alfanata/tictactoe-fpga/vhdl/tictactoe_ram.vhd

-- MIT License
-- 
-- Copyright (c) 2019 J. Tetteroo
-- 
-- Permission is hereby granted, free of charge, to any person obtaining a copy
-- of this software and associated documentation files (the "Software"), to deal
-- in the Software without restriction, including without limitation the rights
-- to use, copy, modify, merge, publish, distribute, sublicense, and/or sell
-- copies of the Software, and to permit persons to whom the Software is
-- furnished to do so, subject to the following conditions:
-- 
-- The above copyright notice and this permission notice shall be included in all
-- copies or substantial portions of the Software.
-- 
-- THE SOFTWARE IS PROVIDED "AS IS", WITHOUT WARRANTY OF ANY KIND, EXPRESS OR
-- IMPLIED, INCLUDING BUT NOT LIMITED TO THE WARRANTIES OF MERCHANTABILITY,
-- FITNESS FOR A PARTICULAR PURPOSE AND NONINFRINGEMENT. IN NO EVENT SHALL THE
-- AUTHORS OR COPYRIGHT HOLDERS BE LIABLE FOR ANY CLAIM, DAMAGES OR OTHER
-- LIABILITY, WHETHER IN AN ACTION OF CONTRACT, TORT OR OTHERWISE, ARISING FROM,
-- OUT OF OR IN CONNECTION WITH THE SOFTWARE OR THE USE OR OTHER DEALINGS IN THE
-- SOFTWARE.

-------------------------------------------------------------------------------
--
-- Title       : tictactoe_ram
-- Design      : tictactoe
-- Author      : J. Tetteroo
-- Year		   : 2019
--
-------------------------------------------------------------------------------

-------------------------------------------------------------------------------
--
-- Description : Memory unit that stores all possible game moves in native BRAM blocks (ice40 512x8) in 3 byte records.
--
-------------------------------------------------------------------------------

library ieee;
library work;
--library ice;	-- uncomment for simulation, comment for synthesis
use ieee.std_logic_1164.all;
--use ice.vcomponent_vital.all; -- uncomment for simulation, comment for synthesis



use work.components.all; 	-- comment for simulation, uncomment for synthesis
use work.tictactoe_global.all;
use ieee.numeric_std.all;

entity tictactoe_ram is
port (
    input : in tictactoe_ram_input_type;
    output : out tictactoe_ram_output_type;
    
    clk : in std_logic;
    reset : in std_logic
    );
end tictactoe_ram;




architecture rtl of tictactoe_ram is 

	-- ### START COMMENT BLOCK FOR SYNTHESIS (comment this block when synthesizing)
	-- Component declaration of the "sb_ram512x8(sb_ram512x8_arch)" unit defined in
	-- file: "./src/sb_ice_syn_vital.vhd"
--	component sb_ram512x8
--	generic(
--		INIT_0 : BIT_VECTOR := X"0000000000000000000000000000000000000000000000000000000000000000";
--		INIT_1 : BIT_VECTOR := X"0000000000000000000000000000000000000000000000000000000000000000";
--		INIT_2 : BIT_VECTOR := X"0000000000000000000000000000000000000000000000000000000000000000";
--		INIT_3 : BIT_VECTOR := X"0000000000000000000000000000000000000000000000000000000000000000";
--		INIT_4 : BIT_VECTOR := X"0000000000000000000000000000000000000000000000000000000000000000";
--		INIT_5 : BIT_VECTOR := X"0000000000000000000000000000000000000000000000000000000000000000";
--		INIT_6 : BIT_VECTOR := X"0000000000000000000000000000000000000000000000000000000000000000";
--		INIT_7 : BIT_VECTOR := X"0000000000000000000000000000000000000000000000000000000000000000";
--		INIT_8 : BIT_VECTOR := X"0000000000000000000000000000000000000000000000000000000000000000";
--		INIT_9 : BIT_VECTOR := X"0000000000000000000000000000000000000000000000000000000000000000";
--		INIT_A : BIT_VECTOR := X"0000000000000000000000000000000000000000000000000000000000000000";
--		INIT_B : BIT_VECTOR := X"0000000000000000000000000000000000000000000000000000000000000000";
--		INIT_C : BIT_VECTOR := X"0000000000000000000000000000000000000000000000000000000000000000";
--		INIT_D : BIT_VECTOR := X"0000000000000000000000000000000000000000000000000000000000000000";
--		INIT_E : BIT_VECTOR := X"0000000000000000000000000000000000000000000000000000000000000000";
--		INIT_F : BIT_VECTOR := X"0000000000000000000000000000000000000000000000000000000000000000"
--	);
--	port(
--		RDATA : out STD_LOGIC_VECTOR(7 downto 0);
--		RCLK : in STD_LOGIC;
--		RCLKE : in STD_LOGIC := 'H';
--		RE : in STD_LOGIC := 'L';
--		RADDR : in STD_LOGIC_VECTOR(8 downto 0);
--		WCLK : in STD_LOGIC;
--		WCLKE : in STD_LOGIC := 'H';
--		WE : in STD_LOGIC := 'L';
--		WADDR : in STD_LOGIC_VECTOR(8 downto 0);
--		WDATA : in STD_LOGIC_VECTOR(7 downto 0)
--	);
--	end component;
--	for all: sb_ram512x8 use entity ice.sb_ram512x8(sb_ram512x8_arch);
	-- ### END COMMENT BLOCK FOR SYNTHESIS
    
    type t_RDATA_a is array (0 to 27) of std_logic_vector(7 downto 0);
    type t_RADDR_a is array (0 to 27) of std_logic_vector(8 downto 0);
    subtype t_RADDR is std_logic_vector(8 downto 0);
    subtype t_RCLKE is std_logic_vector(27 downto 0);
    subtype t_RE is std_logic_vector(27 downto 0);
    
    type state_type is (st_set_addr, st_wait_1, st_read_1, st_wait_2, st_read_2, st_wait_3, st_read_3, st_check, st_match, st_no_match);
    
    type reg_type is record
        match : std_logic;
        perm_block : natural range 0 to 27;      -- BRAM block
        perm_addr : natural range 0 to 511;       -- address within BRAM
		
        board_config : std_logic_vector(17 downto 0);
        output_move : std_logic_vector(3 downto 0);
        state : state_type;
	end record;
    
    signal r, rin : reg_type := (match => '0',
								perm_block => 0,
								perm_addr => 0,
								board_config => (others => '0'),
								output_move => (others => '0'),
								state => st_set_addr);
    
    signal RDATA_a : t_RDATA_a := (others => (others => '0'));
    signal RADDR_c : t_RADDR :=  (others => '0');
    signal RCLKE_c : t_RCLKE := (others => '0');
    signal RE_c : t_RE := (others => '0');
    signal RCLK_c : std_logic := '0';
    
    -- RADDR can fan out to each BRAM, we only read the relevant block, could be inefficient

begin
ram512x8_inst_0 : SB_RAM512X8
generic map (
INIT_0 => X"204000A02400802000C012008010008004002022004010004001002004000000",
INIT_1 => X"4801803001802401801301202001002401401101001001000200604000404000",
INIT_2 => X"00C08800A0800080800060800040840020840120600140540140400120400100",
INIT_3 => X"80300280200280120220200200200240110200100200000060C400A0A000C090",
INIT_4 => X"5303004303803003003303002003001302206002405102404102204002004002",
INIT_5 => X"0280920280800220A00240910240800220800200800320600300630340500300",
INIT_6 => X"A1070081000061060041000021000260C00240C00220C002A0A00280A002C092",
INIT_7 => X"1001810101212201411001410201210201010000614200A12100C11000C10800",
INIT_8 => X"04000000C18300A18300618601614201414201214201A12101812101C1100181",
INIT_9 => X"4054044041042044040042048030048020048010042024040024044012040016",
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
INIT_F => X"0000000000000000000000000000000000000000000000000000000000000000"
)
port map (
RDATA => RDATA_a(26),
RADDR => RADDR_c,
RCLK => RCLK_c,
RCLKE => RCLKE_c(26),
RE => RE_c(26),
WADDR => (others => '0'),
WCLK=> '0',
WCLKE => '0',
WDATA => (others => '0'),
WE => '0'
);
    combinatorial : process(reset, r, RDATA_a)
	    variable v : reg_type;
    
        variable block_addr : natural range 0 to 14508; -- NUM_RECORDS=4836*3
        variable block_select : natural range 0 to 27;  -- NUM_BLOCKS
        variable block_idx : natural range 0 to 511;    -- BLOCK_SIZE
        variable block_buf : std_logic_vector(7 downto 0);
    
        begin
            v := r;
            
            block_addr := input.perm_idx * 3;
            block_select := block_addr / 512;   -- synthesizer bitshift
            block_idx := block_addr mod 512;
        
            case (r.state) is
                when st_set_addr =>
					v.board_config := "000000000000000000";
                    v.perm_block := block_select;
                    v.perm_addr := block_idx;
					
                    v.state := st_read_1;
                when st_read_1 =>
					v.board_config := "00000000000000" & RDATA_a(r.perm_block)(7 downto 4);
					--v.board_config := "0000000000" & RDATA_a(r.perm_block);
					v.output_move := RDATA_a(r.perm_block)(3 downto 0);
					
					v.perm_addr := (r.perm_addr + 1) mod 512;
				    if r.perm_addr = 511 then
                        v.perm_block := r.perm_block + 1;
                  	end if;
					  
                    v.state := st_read_2;
                when st_read_2 =>
					v.board_config := "000000" & RDATA_a(r.perm_block) & r.board_config(3 downto 0);
					--v.board_config := "0000000000" & RDATA_a(r.perm_block);
					
					v.perm_addr := (r.perm_addr + 1) mod 512;
				    if r.perm_addr = 511 then
                        v.perm_block := r.perm_block + 1;
                  	end if;
                    v.state := st_read_3;
                when st_read_3 =>
					v.board_config := RDATA_a(r.perm_block)(5 downto 0) & r.board_config(11 downto 0);
					--v.board_config := "0000000000" & RDATA_a(r.perm_block);
					
                    
                    v.state := st_check;
                when st_check =>					
                    if (v.board_config = (input.board_p1 & input.board_p2)) then
                        v.state := st_match;
                    else
                        v.state := st_no_match;
                    end if;
					
                when st_match =>
					v.state := st_match;
				
                when st_no_match =>
					v.state := st_no_match;
				when others =>
					v.state := st_set_addr;
                
                    
            end case;
			
			if (reset = '1') then
				v.state := st_set_addr;
			end if;
            
            RADDR_c <= std_logic_vector(to_unsigned(v.perm_addr, 9));
			
            RCLKE_c <= (others => '0');
            RCLKE_c(v.perm_block) <= '1';
			RCLKE_c(v.perm_block+1) <= '1';	-- enable the next block in case it overlaps, easiest but not optimal solution
			
            RE_c <= (others => '0');
            RE_c(v.perm_block) <= '1';
			RE_c(v.perm_block+1) <= '1';
			
            
            output.match <= '1' when (r.state = st_match) else '0';
            output.done <= '1' when (r.state = st_match OR r.state = st_no_match) else '0';
            output.output_move <= r.output_move;
			rin <= v;
            
    end process;

	synchronous : process(clk)
	begin
		if clk'event and clk = '1' then
			r <= rin;
		end if;
	end process;  
	
	RCLK_c <= clk;
    
end rtl;
