alfanata/tictactoe-fpga/vhdl/tictactoe_ram_tb.vhd

-- MIT License
-- 
-- Copyright (c) 2019 J. Tetteroo
-- 
-- Permission is hereby granted, free of charge, to any person obtaining a copy
-- of this software and associated documentation files (the "Software"), to deal
-- in the Software without restriction, including without limitation the rights
-- to use, copy, modify, merge, publish, distribute, sublicense, and/or sell
-- copies of the Software, and to permit persons to whom the Software is
-- furnished to do so, subject to the following conditions:
-- 
-- The above copyright notice and this permission notice shall be included in all
-- copies or substantial portions of the Software.
-- 
-- THE SOFTWARE IS PROVIDED "AS IS", WITHOUT WARRANTY OF ANY KIND, EXPRESS OR
-- IMPLIED, INCLUDING BUT NOT LIMITED TO THE WARRANTIES OF MERCHANTABILITY,
-- FITNESS FOR A PARTICULAR PURPOSE AND NONINFRINGEMENT. IN NO EVENT SHALL THE
-- AUTHORS OR COPYRIGHT HOLDERS BE LIABLE FOR ANY CLAIM, DAMAGES OR OTHER
-- LIABILITY, WHETHER IN AN ACTION OF CONTRACT, TORT OR OTHERWISE, ARISING FROM,
-- OUT OF OR IN CONNECTION WITH THE SOFTWARE OR THE USE OR OTHER DEALINGS IN THE
-- SOFTWARE.

-------------------------------------------------------------------------------
--
-- Title       : tictactoe_ram_tb
-- Design      : tictactoe
-- Author      : J. Tetteroo
-- Year		   : 2019
--
-------------------------------------------------------------------------------

-------------------------------------------------------------------------------
--
-- Description : testbench for tictactoe_ram entity, tests all valid board configurations
--
-------------------------------------------------------------------------------

library ieee;
library work;
use ieee.std_logic_1164.all;
use ieee.numeric_std.all;
use work.tictactoe_global.all;
use work.tictactoe_ram;


entity tictactoe_ram_tb is
end tictactoe_ram_tb;


architecture test of tictactoe_ram_tb is

    constant DELTA : time := 100 ns;


    signal sim_finished : boolean := false;

    signal clk : std_logic;
    signal reset : std_logic;

    
    signal ram_input : tictactoe_ram_input_type;

    signal ram_output : tictactoe_ram_output_type;


begin
    -- ram instance
    tttram : entity tictactoe_ram
        port map(clk => clk,
                reset => reset,
                input => ram_input,
                output => ram_output);
          
    -- Test
    clock : process
    begin
        if not sim_finished then
            clk <= '1';
            wait for DELTA / 2;
            clk <= '0';
            wait for DELTA / 2;
        else
            wait;
        end if;
    end process clock;
    
    
    simulation : process
	
		procedure check_mem(constant rec_in: in natural;
							constant board_p1 : in std_logic_vector(8 downto 0);
							constant board_p2 : in std_logic_vector(8 downto 0);
							constant next_move : in natural;
							constant is_match : in std_logic) is
			variable output_move : natural;
		begin
			-- state set_addr
			ram_input.perm_idx <= rec_in;
			ram_input.board_p1 <= board_p1;
			ram_input.board_p2 <= board_p2;
			
			wait until rising_edge(clk);
			-- state read 1
			assert ram_output.done = '0' report "Operation completed prematurely" severity error;
			
        	wait until rising_edge(clk);
			-- state read 2
			assert ram_output.done = '0' report "Operation completed prematurely" severity error;
			
			wait until rising_edge(clk);
			-- state read 3
			assert ram_output.done = '0' report "Operation completed prematurely" severity error;
			
			
			wait until rising_edge(clk);
			-- state check
			assert ram_output.done = '0' report "Operation completed prematurely" severity error;
			
			-- state match/no_match
        	wait until rising_edge(clk);
			wait for DELTA / 4;
			output_move := to_integer(unsigned(ram_output.output_move));
			assert ram_output.done = '1' report "Operation not completed: " & integer'image(rec_in) severity error;
			assert ram_output.match = is_match report "Match signal mismatch: " & integer'image(rec_in) severity error;
			assert output_move = next_move report "Incorrect output move: " & integer'image(rec_in) severity error;
			
		end procedure;
		
		procedure sync_reset is
		begin
			wait until rising_edge(CLK);
			wait for DELTA / 4;
			reset <= '1';
			wait until rising_edge(CLK);
			wait for DELTA / 4;
			reset <= '0';
		end procedure sync_reset;

		variable init_input : tictactoe_ram_input_type;
    begin
		
		init_input.perm_idx := 0;
		init_input.board_p1 := "000000000";
		init_input.board_p2 := "000000000";

		ram_input <= init_input;
		reset <= '0';
		
        wait for DELTA;
		
		report "#### START TESTS ####";
sync_reset;
check_mem(0,"000000000","000000000",0,'1'); -- (0, 0, 0, 0, 0, 0, 0, 0, 0)
sync_reset;
check_mem(1,"000000001","000000000",4,'1'); -- (0, 0, 0, 0, 0, 0, 0, 0, 1)
sync_reset;
check_mem(2,"000000010","000000000",1,'1'); -- (0, 0, 0, 0, 0, 0, 0, 1, 0)
sync_reset;
check_mem(3,"000000010","000000001",0,'1'); -- (0, 0, 0, 0, 0, 0, 0, 1, 2)
sync_reset;
check_mem(4,"000000001","000000010",2,'1'); -- (0, 0, 0, 0, 0, 0, 0, 2, 1)
sync_reset;
check_mem(5,"000000100","000000000",4,'1'); -- (0, 0, 0, 0, 0, 0, 1, 0, 0)
sync_reset;
check_mem(6,"000000100","000000001",0,'1'); -- (0, 0, 0, 0, 0, 0, 1, 0, 2)
sync_reset;
check_mem(7,"000000110","000000001",2,'1'); -- (0, 0, 0, 0, 0, 0, 1, 1, 2)
sync_reset;
check_mem(8,"000000100","000000010",0,'1'); -- (0, 0, 0, 0, 0, 0, 1, 2, 0)
sync_reset;
check_mem(9,"000000101","000000010",4,'1'); -- (0, 0, 0, 0, 0, 0, 1, 2, 1)
sync_reset;
check_mem(10,"000000001","000000100",0,'1'); -- (0, 0, 0, 0, 0, 0, 2, 0, 1)
sync_reset;
check_mem(11,"000000010","000000100",0,'1'); -- (0, 0, 0, 0, 0, 0, 2, 1, 0)
sync_reset;
check_mem(12,"000000011","000000100",0,'1'); -- (0, 0, 0, 0, 0, 0, 2, 1, 1)
sync_reset;
check_mem(13,"000001000","000000000",2,'1'); -- (0, 0, 0, 0, 0, 1, 0, 0, 0)
sync_reset;
check_mem(14,"000001000","000000001",0,'1'); -- (0, 0, 0, 0, 0, 1, 0, 0, 2)
sync_reset;
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
sync_reset;
check_mem(1285,"010010001","001100010",0,'1'); -- (0, 1, 2, 2, 1, 0, 0, 2, 1)
sync_reset;
check_mem(1286,"010010100","001100000",7,'1'); -- (0, 1, 2, 2, 1, 0, 1, 0, 0)
sync_reset;
check_mem(1287,"010010100","001100001",7,'1'); -- (0, 1, 2, 2, 1, 0, 1, 0, 2)
sync_reset;
check_mem(1288,"010010100","001100010",0,'1'); -- (0, 1, 2, 2, 1, 0, 1, 2, 0)
sync_reset;
check_mem(1289,"010010101","001100010",0,'1'); -- (0, 1, 2, 2, 1, 0, 1, 2, 1)
sync_reset;
check_mem(1290,"010010001","001100100",0,'1'); -- (0, 1, 2, 2, 1, 0, 2, 0, 1)
sync_reset;
check_mem(1291,"010011000","001100000",7,'1'); -- (0, 1, 2, 2, 1, 1, 0, 0, 0)
sync_reset;
check_mem(1292,"010011000","001100001",7,'1'); -- (0, 1, 2, 2, 1, 1, 0, 0, 2)
sync_reset;
check_mem(1293,"010011000","001100010",0,'1'); -- (0, 1, 2, 2, 1, 1, 0, 2, 0)
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
